jssanshi/DeepBot/models/object_detection/data/images/traffic/validation/images/camera_050.jpg

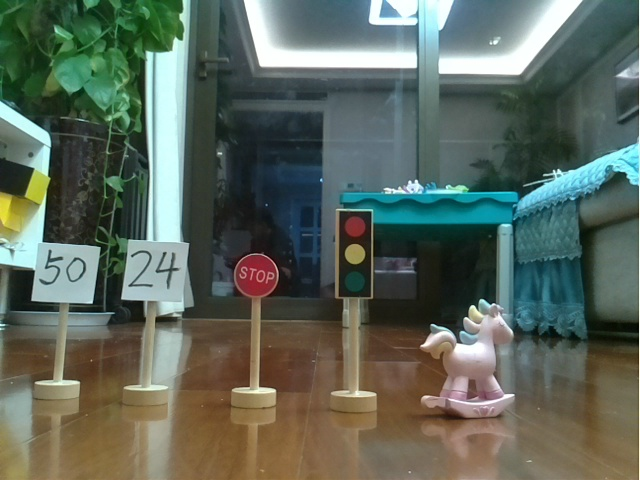
models/object_detection/data/images/traffic/validation/images/camera_050.jpg
