jssanshi/DeepBot/models/object_detection/data/images/mario/validation/images/snapshot_1753587024.jpg

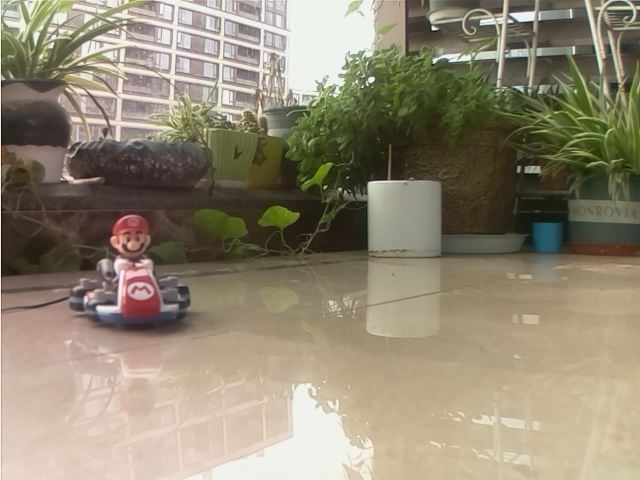
models/object_detection/data/images/mario/validation/images/snapshot_1753587024.jpg
