jssanshi/DeepBot/models/object_detection/data/images/mario/validation/images/snapshot_1753587019.jpg

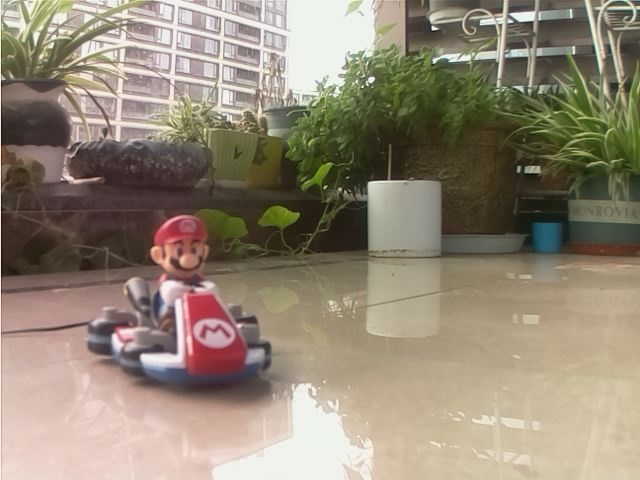
models/object_detection/data/images/mario/validation/images/snapshot_1753587019.jpg
