jssanshi/DeepBot/models/object_detection/data/images/traffic/test/images/camera_002.jpg

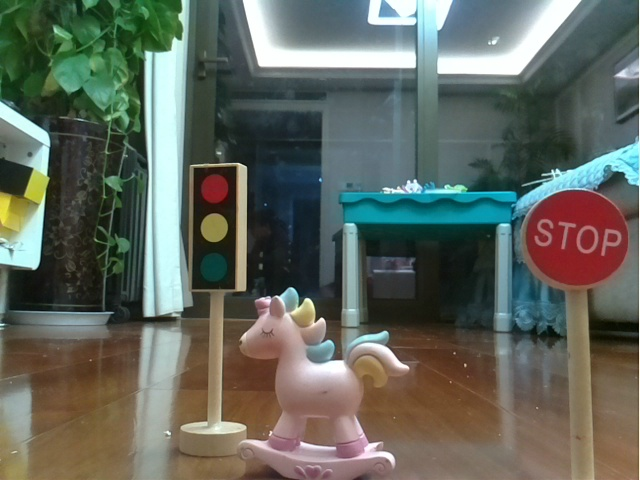
models/object_detection/data/images/traffic/test/images/camera_002.jpg
