jssanshi/DeepBot/models/object_detection/data/images/traffic/validation/images/camera_048.jpg

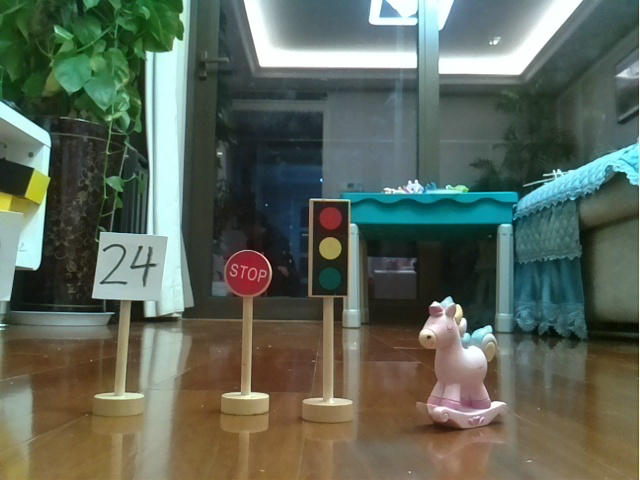
models/object_detection/data/images/traffic/validation/images/camera_048.jpg
